reubenstr/RGBY-ROM/stl/RGBY-ROM-nameplate-bezel.stl

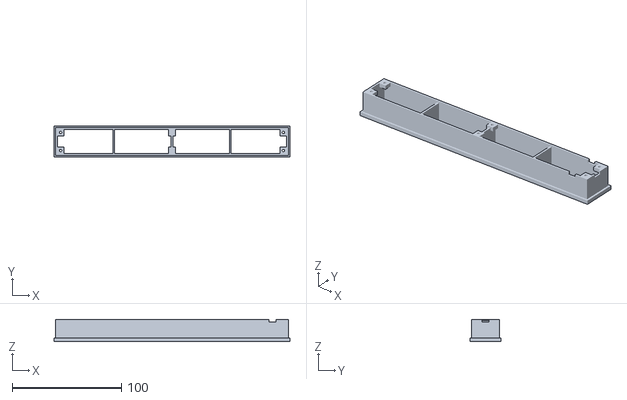
[picture p18: CAD file, 2021-03-17]
stl/RGBY-ROM-nameplate-bezel.stl
215.7 x 28.6 x 20.2
