reubenstr/RGBY-ROM/stl/RGBY-ROM-data-cartridge-a.stl

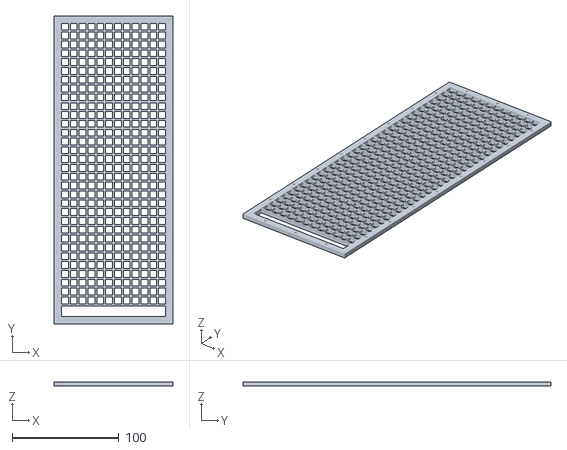
[picture p19: CAD file, 2021-03-17]
stl/RGBY-ROM-data-cartridge-a.stl
110.9 x 288.0 x 4.19
