reubenstr/RGBY-ROM/stl/RGBY-ROM-bearing-block.stl

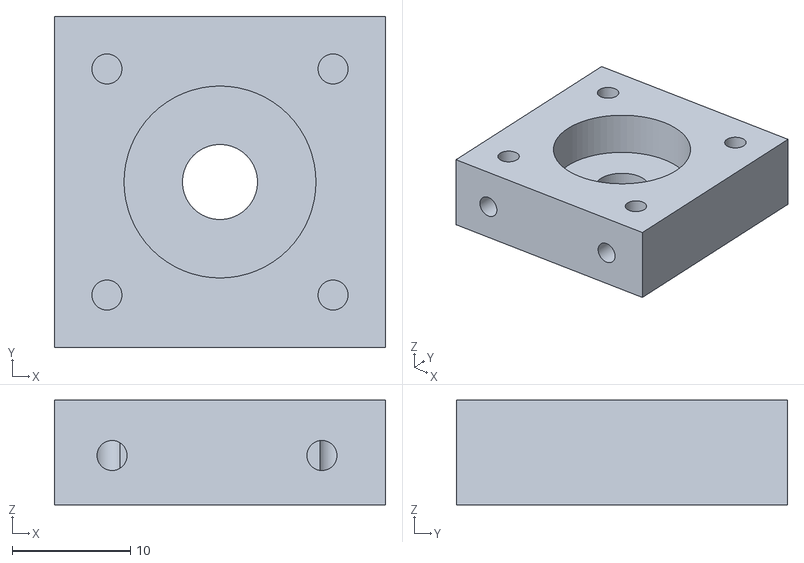
[picture p20: CAD file, 2021-03-17]
stl/RGBY-ROM-bearing-block.stl
28.0 x 28.0 x 8.89
