reubenstr/RGBY-ROM/stl/RGBY-ROM-sensor-truck-channel-cap.stl

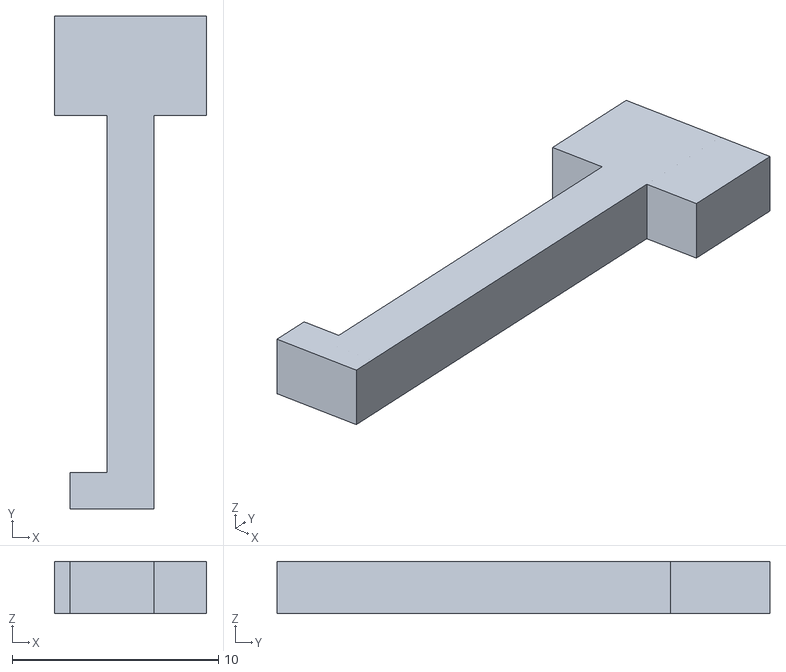
[picture p21: CAD file, 2021-03-17]
stl/RGBY-ROM-sensor-truck-channel-cap.stl
7.37 x 23.9 x 2.54
