reubenstr/RGBY-ROM/stl/RGBY-ROM-riser-b.stl

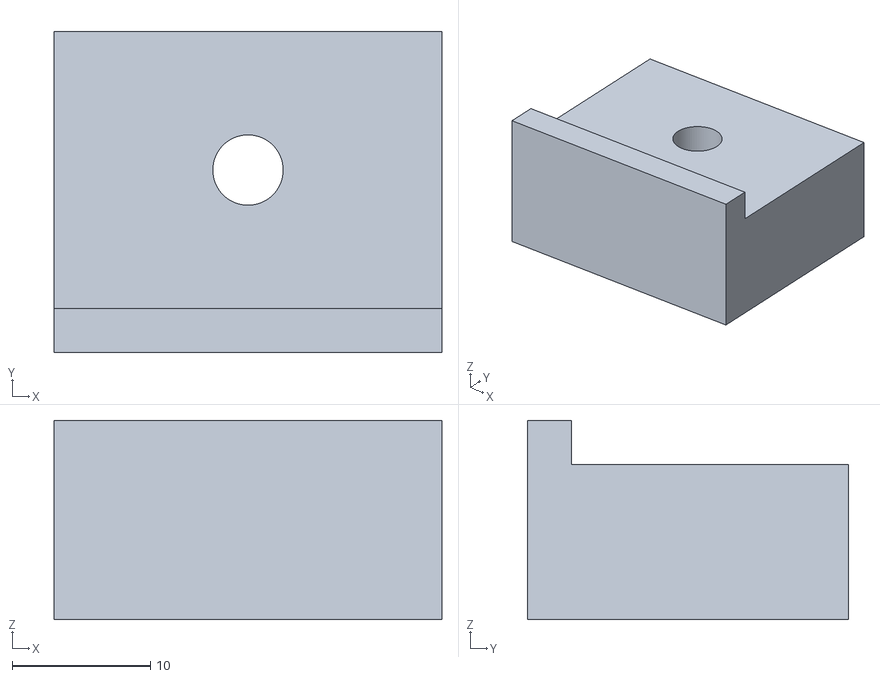
[picture p22: CAD file, 2021-03-17]
stl/RGBY-ROM-riser-b.stl
28.0 x 23.2 x 14.4
