reubenstr/RGBY-ROM/stl/RGBY-ROM-idler-mounting-bracket.stl

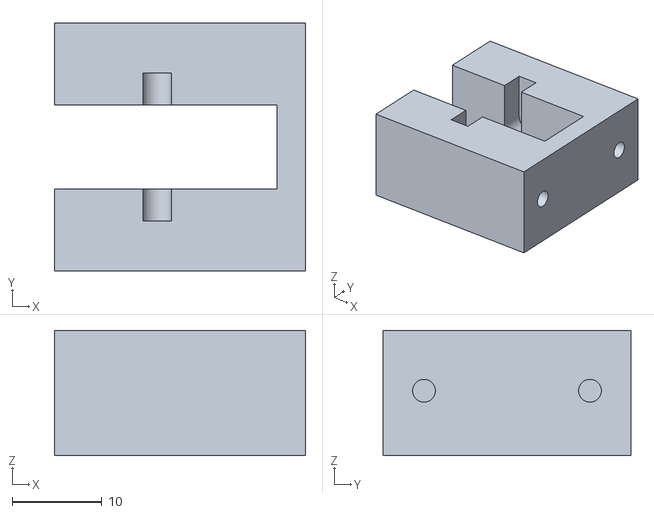
[picture p23: CAD file, 2021-03-17]
stl/RGBY-ROM-idler-mounting-bracket.stl
28.0 x 27.7 x 14.0
