reubenstr/RGBY-ROM/stl/RGBY-ROM-led-bezel-holddown-clip.stl

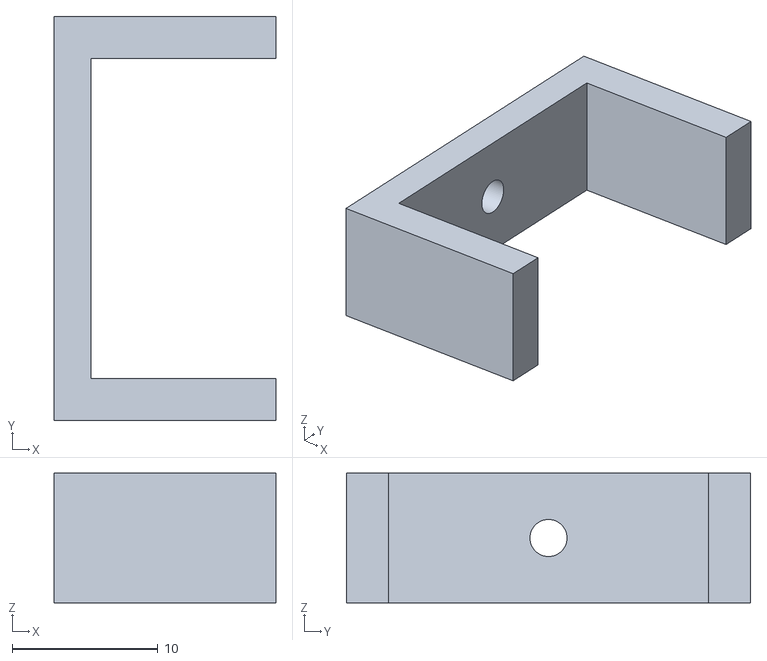
[picture p24: CAD file, 2021-03-17]
stl/RGBY-ROM-led-bezel-holddown-clip.stl
15.2 x 27.8 x 8.89
