reubenstr/RGBY-ROM/stl/RGBY-ROM-rgb-led-bezel-holding-clip.stl

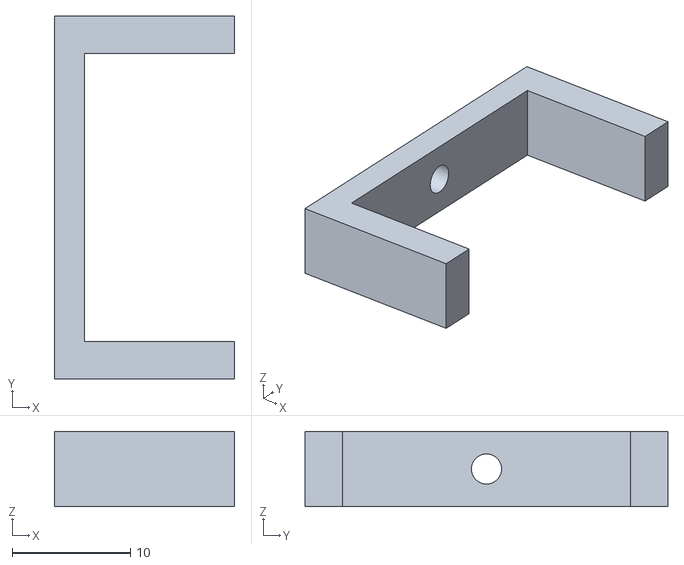
[picture p25: CAD file, 2021-03-17]
stl/RGBY-ROM-rgb-led-bezel-holding-clip.stl
15.2 x 30.7 x 6.35
