reubenstr/RGBY-ROM/stl/RGBY-ROM-tact-switch-holddown.stl

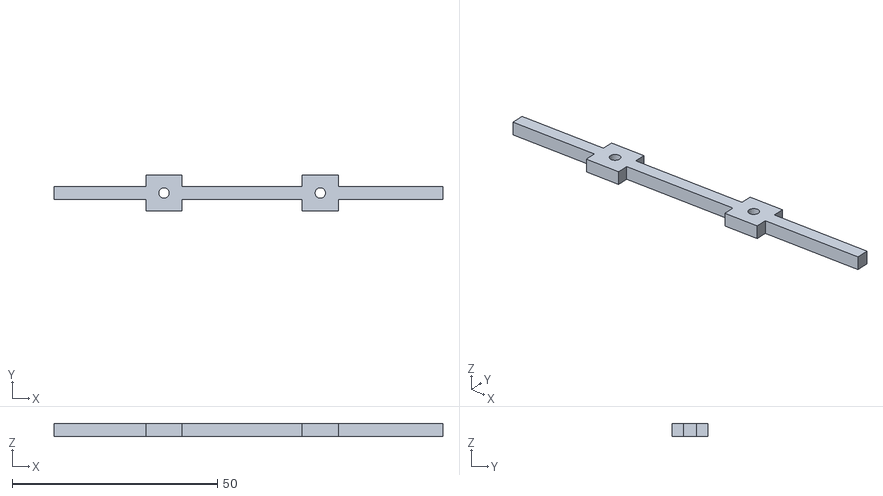
[picture p26: CAD file, 2021-03-17]
stl/RGBY-ROM-tact-switch-holddown.stl
94.8 x 8.89 x 3.17
