reubenstr/RGBY-ROM/stl/RGBY-ROM-sensor-shield.stl

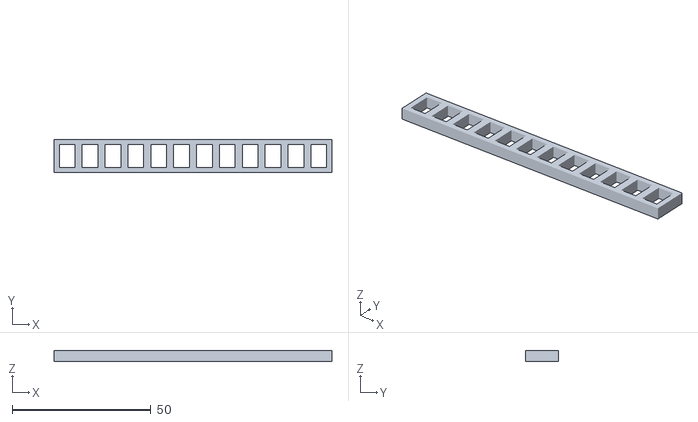
[picture p27: CAD file, 2021-03-17]
stl/RGBY-ROM-sensor-shield.stl
100.3 x 12.1 x 3.81
