reubenstr/RGBY-ROM/stl/RGBY-ROM-rgb-led-bezel.stl

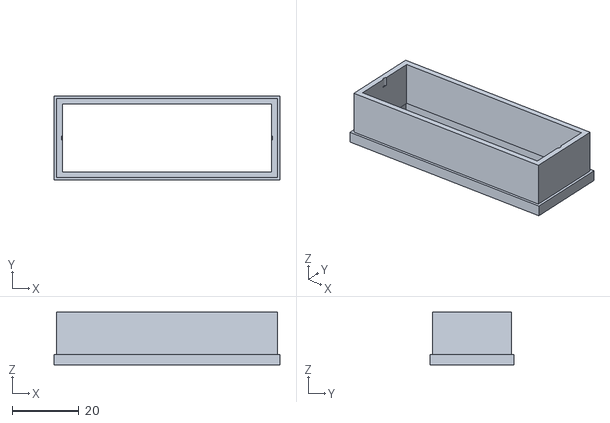
[picture p28: CAD file, 2021-03-17]
stl/RGBY-ROM-rgb-led-bezel.stl
67.9 x 25.4 x 15.9
