reubenstr/RGBY-ROM/stl/RGBY-ROM-ribbon-cable-holding-bracket.stl

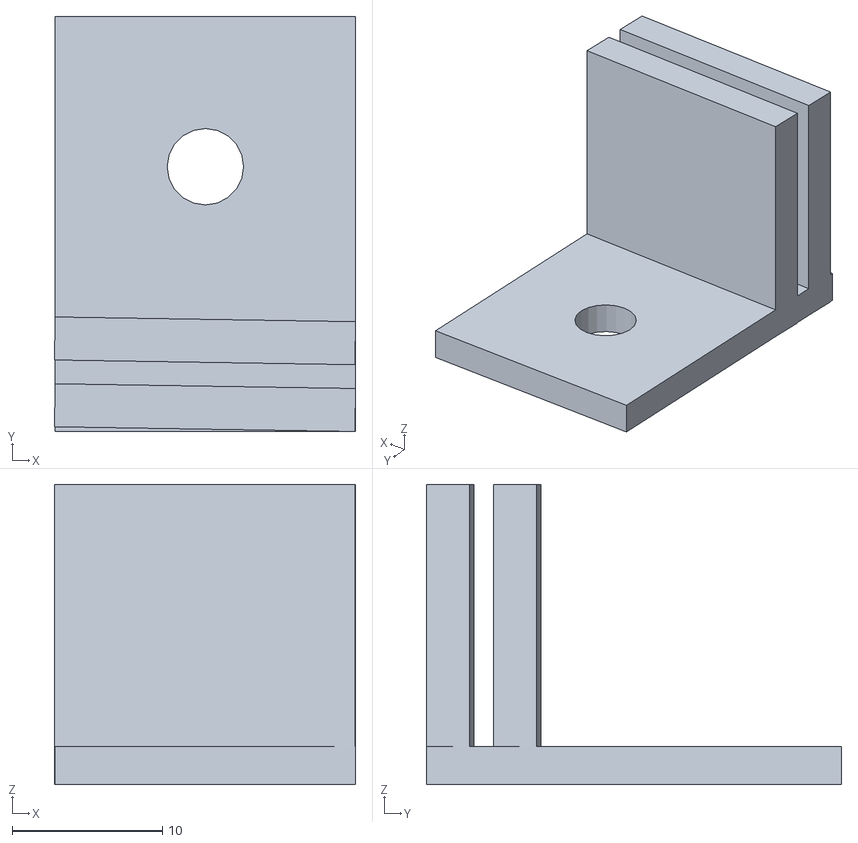
[picture p29: CAD file, 2021-03-17]
stl/RGBY-ROM-ribbon-cable-holding-bracket.stl
20.0 x 27.6 x 20.0
