reubenstr/RGBY-ROM/stl/RGBY-ROM-wire-mounting-bracket.stl

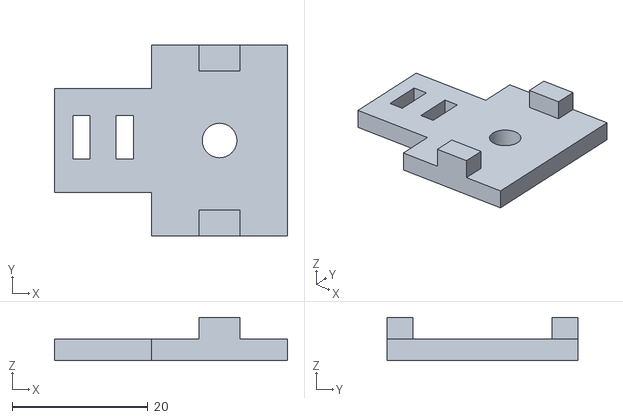
[picture p30: CAD file, 2021-03-17]
stl/RGBY-ROM-wire-mounting-bracket.stl
34.3 x 28.0 x 6.35
