reubenstr/RGBY-ROM/stl/RGBY-ROM-data-cartridge-b.stl

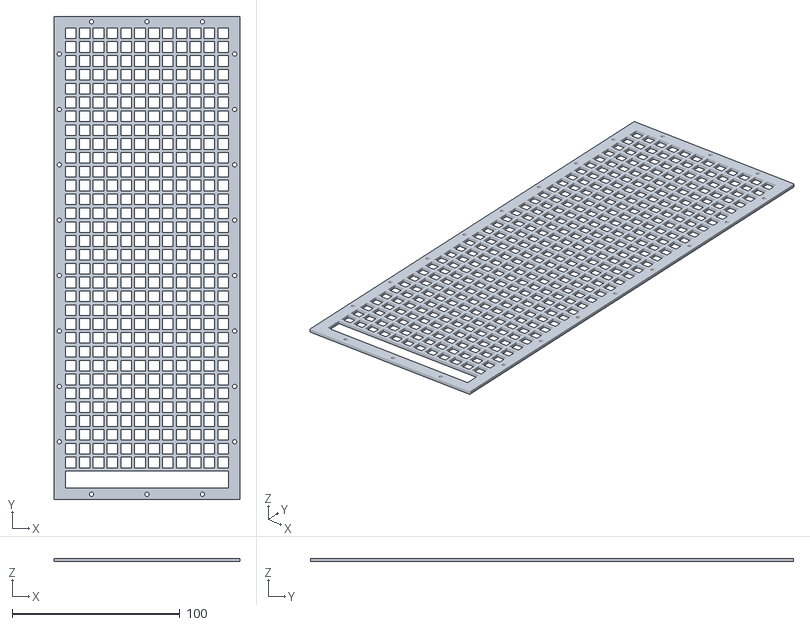
[picture p31: CAD file, 2021-03-17]
stl/RGBY-ROM-data-cartridge-b.stl
110.9 x 288.0 x 1.90
