reubenstr/RGBY-ROM/stl/RGBY-ROM-sensor-truck-no-wire-channel.stl

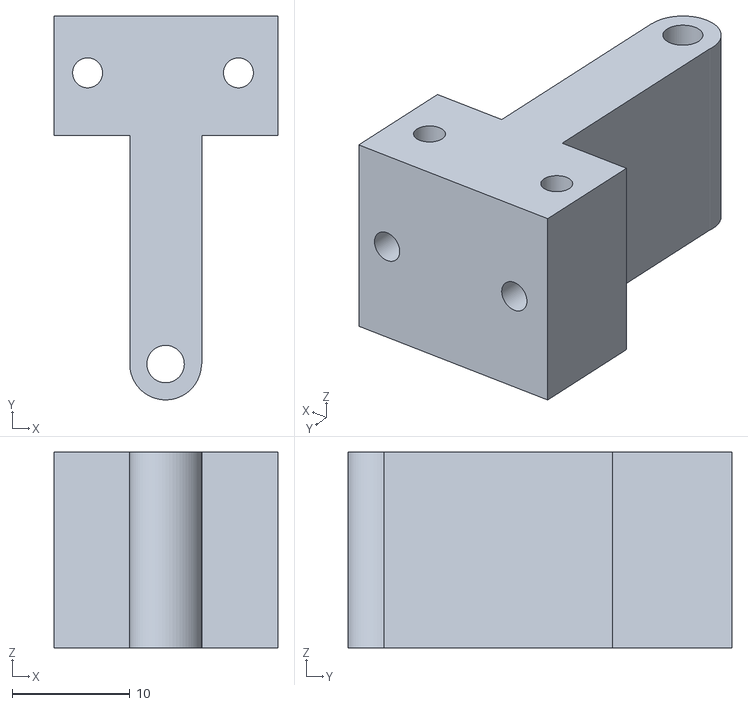
[picture p32: CAD file, 2021-03-17]
stl/RGBY-ROM-sensor-truck-no-wire-channel.stl
19.0 x 32.6 x 16.6
