reubenstr/RGBY-ROM/stl/RGBY-ROM-sensor-truck-wiring-channel.stl

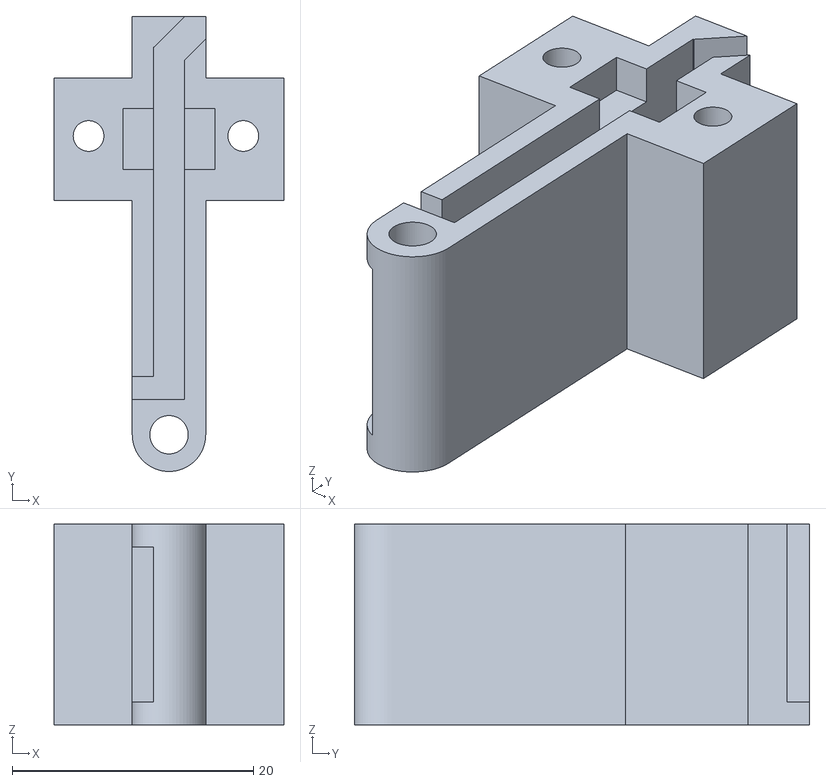
[picture p33: CAD file, 2021-03-17]
stl/RGBY-ROM-sensor-truck-wiring-channel.stl
19.1 x 37.7 x 16.6
