reubenstr/RGBY-ROM/FPGA/sinTable.v

// Convert 8-bit value into sinusoid equivalent.
// Generated from generateSin.py

module sinTable(
input [7:0] in,
output [7:0] out);

assign out =
	(in == 0) ? 0 :
	(in == 1) ? 0 :
	(in == 2) ? 0 :
	(in == 3) ? 0 :
	(in == 4) ? 0 :
	(in == 5) ? 0 :
	(in == 6) ? 0 :
	(in == 7) ? 0 :
	(in == 8) ? 1 :
	(in == 9) ? 1 :
	(in == 10) ? 1 :
	(in == 11) ? 1 :
	(in == 12) ? 1 :
	(in == 13) ? 2 :
	(in == 14) ? 2 :
	(in == 15) ? 2 :
	(in == 16) ? 2 :
	(in == 17) ? 3 :
	(in == 18) ? 3 :
	(in == 19) ? 3 :
	(in == 20) ? 4 :
	(in == 21) ? 4 :
	(in == 22) ? 5 :
	(in == 23) ? 5 :
	(in == 24) ? 5 :
	(in == 25) ? 6 :
	(in == 26) ? 6 :
	(in == 27) ? 7 :
	(in == 28) ? 7 :
	(in == 29) ? 8 :
	(in == 30) ? 9 :
	(in == 31) ? 9 :
	(in == 32) ? 10 :
	(in == 33) ? 10 :
	(in == 34) ? 11 :
	(in == 35) ? 12 :
	(in == 36) ? 12 :
	(in == 37) ? 13 :
	(in == 38) ? 14 :
	(in == 39) ? 14 :
	(in == 40) ? 15 :
	(in == 41) ? 16 :
	(in == 42) ? 17 :
	(in == 43) ? 17 :
	(in == 44) ? 18 :
	(in == 45) ? 19 :
	(in == 46) ? 20 :
	(in == 47) ? 21 :
	(in == 48) ? 21 :
	(in == 49) ? 22 :
	(in == 50) ? 23 :
	(in == 51) ? 24 :
	(in == 52) ? 25 :
	(in == 53) ? 26 :
	(in == 54) ? 27 :
	(in == 55) ? 28 :
	(in == 56) ? 29 :
	(in == 57) ? 30 :
	(in == 58) ? 31 :
	(in == 59) ? 32 :
	(in == 60) ? 33 :
	(in == 61) ? 34 :
	(in == 62) ? 35 :
	(in == 63) ? 36 :
	(in == 64) ? 37 :
	(in == 65) ? 38 :
	(in == 66) ? 40 :
	(in == 67) ? 41 :
	(in == 68) ? 42 :
	(in == 69) ? 43 :
	(in == 70) ? 44 :
	(in == 71) ? 45 :
	(in == 72) ? 47 :
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
	(in == 243) ? 253 :
	(in == 244) ? 254 :
	(in == 245) ? 254 :
	(in == 246) ? 254 :
	(in == 247) ? 254 :
	(in == 248) ? 254 :
	(in == 249) ? 255 :
	(in == 250) ? 255 :
	(in == 251) ? 255 :
	(in == 252) ? 255 :
	(in == 253) ? 255 :
	(in == 254) ? 255 :
	(in == 255) ? 255 :
	0;
endmodule
